pshersby/HP-Cal/Data/Connector.PNG

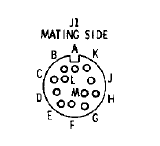
Data/Connector.PNG
