pshersby/HP-Cal/Data/Voltage divider.JPG

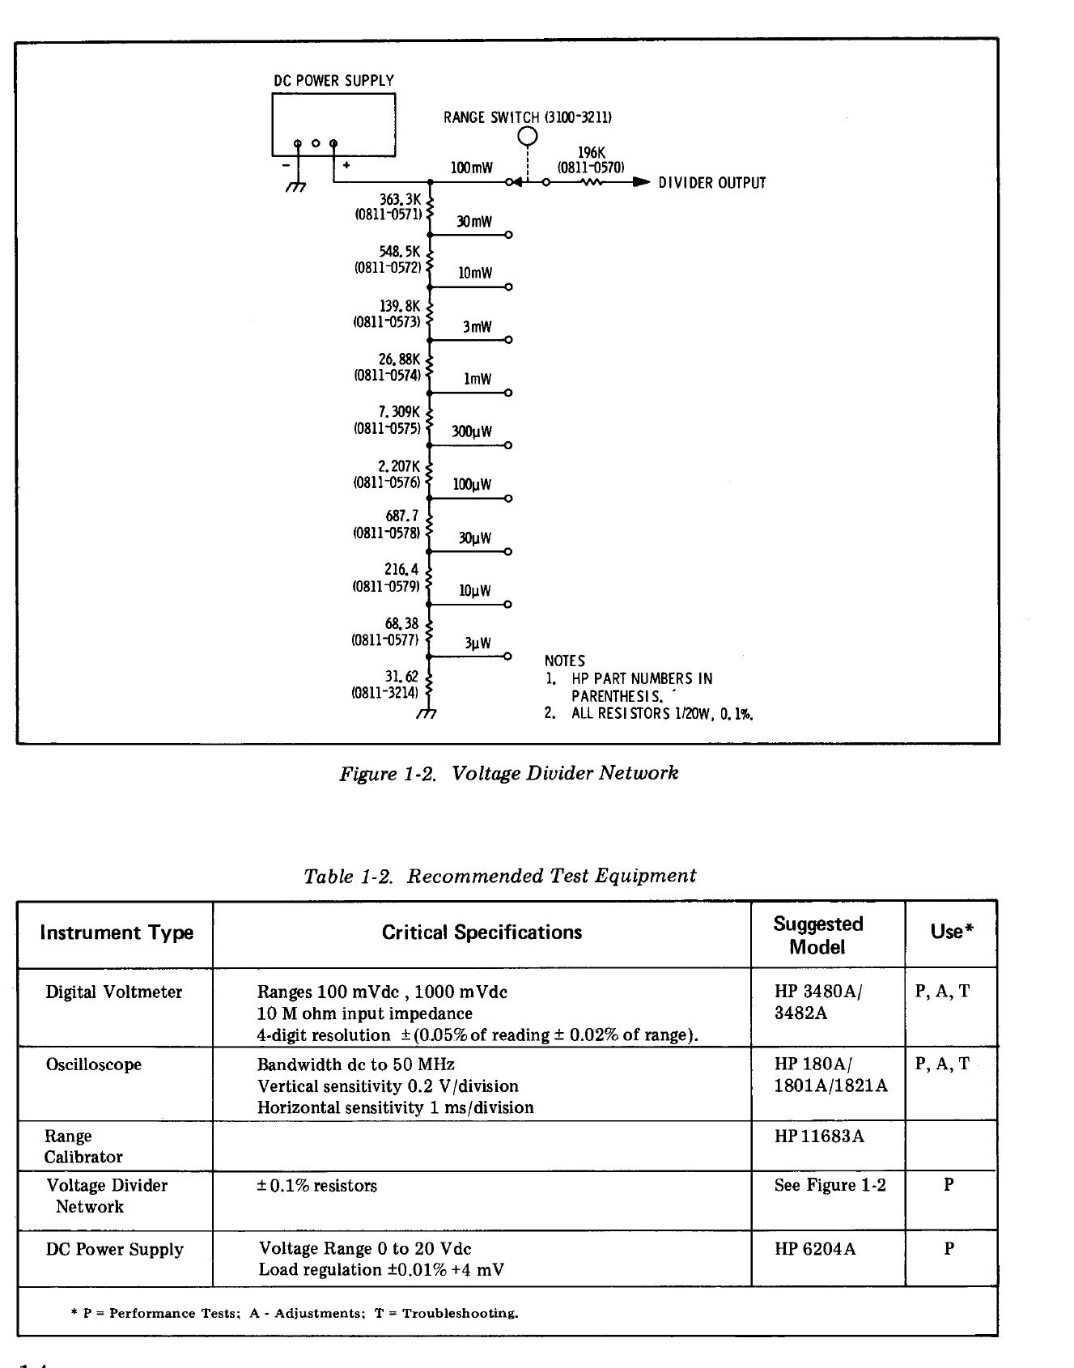
Data/Voltage divider.JPG
