pshersby/HP-Cal/DividerSimulation.cir

[Main]
FileType=CIR
Version=12.00
Program=Micro-Cap
Component Version=10.00
Shape Version=11.00
Screen=2560,1440
MCAPVersion=12.0.2.1
Key ID=Demo
NLCnt=43
TXCnt=4

[shapedef]
Name=Battery
Line=0,0,22,0
Line=22,-3,22,3
Line=26,-7,26,7
Line=26,0,48,0
Current=32,8,16,8

[shapedef]
Name=Ground
Line=0,0,12,0
Line=12,-8,12,8
Line=18,-4,18,4
Line=24,0,24,0

[shapedef]
Name=Resistor
PolyOpen=12
PolyLine=0,0
PolyLine=0,0
PolyLine=12,0
PolyLine=14,-4
PolyLine=18,4
PolyLine=22,-4
PolyLine=26,4
PolyLine=30,-4
PolyLine=34,4
PolyLine=36,0
PolyLine=48,0
PolyLine=48,0
Current=32,8,16,8

[compdef]
Name=Resistor
Definition=Resistor
Shape=Resistor
Mask=7425
Used=162
memo=Resistor
Label Offset=18,6,8,11
PinCnt=2
Pin="Plus",6,0,-10,-4
Pin="Minus",0,0,-14,-4

[compdef]
Name=Ground
Definition=Ground
Shape=Ground
Mask=1793
Used=259
memo=Ground
Label Offset=0,0,0,0
PinCnt=1
Pin="PinA",0,0,-3,-7

[compdef]
Name=Battery
Definition=Battery
Shape=Battery
Mask=6913
Used=52
memo=Battery
Label Offset=19,7,10,13
PinCnt=2
Pin="Plus",6,0,-4,-5
Pin="Minus",0,0,-10,-5

[Circuit]
Window Placement=2,3, -1,-1, -8,-31, 0,0,1961,813
Default Object=Color=#000080
Default Object Font=Height=-15,FStyle=0,Color=#000080,Name=Arial
Default Object Apply Border To Text=No
Default Object Apply Fill To Text=No
Default Object GridSnap=No
NodeVoltageFormat=3
CurrentFormat=3
PowerFormat=3
PathDelayFormat=3
WarningFormat=3
GridTextFormulaFormat=3
Window Placement in Transient Analysis=2,3, -1,-1, -8,-31, 0,0,1961,813
Window Placement in DC Analysis=2,3, -1,-1, -8,-31, 26,26,2187,824
SpiceType=AMBIGUOUS
Title_Block_Border=None
Title_Block=False
Show Nodes=False
Show Voltages=False
Show Current=False
Show Power=False
Show Condition=False
Show Pin Connections=False
Show Connection Warnings=False
Show Cross=False
Show Attribute Text=True
Show Grid Text=True

[Comp]
Name=Resistor
Px=832,280
Rot=3

[Attr]
ON=-24,-25,PART
V=R1
Style=8192

[Attr]
ON=-51,-39,RESISTANCE
V=363.3k
Style=8192

[Attr]
ON=0,0,PACKAGE
V

[Comp]
Name=Resistor
Px=832,352
Rot=3

[Attr]
ON=-24,-25,PART
V=R2
Style=8192

[Attr]
ON=-51,-39,RESISTANCE
V=548.5k
Style=8192

[Attr]
ON=0,0,PACKAGE
V

[Comp]
Name=Resistor
Px=832,440
Rot=3

[Attr]
ON=-24,-25,PART
V=R3
Style=8192

[Attr]
ON=-51,-39,RESISTANCE
V=139.8k
Style=8192

[Attr]
ON=0,0,PACKAGE
V

[Comp]
Name=Resistor
Px=832,528
Rot=3

[Attr]
ON=-24,-25,PART
V=R4
Style=8192

[Attr]
ON=-51,-39,RESISTANCE
V=26.88k
Style=8192

[Attr]
ON=0,0,PACKAGE
V

[Comp]
Name=Resistor
Px=832,608
Rot=3

[Attr]
ON=-24,-25,PART
V=R5
Style=8192

[Attr]
ON=-51,-39,RESISTANCE
V=7.309k
Style=8192

[Attr]
ON=0,0,PACKAGE
V

[Comp]
Name=Resistor
Px=832,704
Rot=3

[Attr]
ON=-24,-25,PART
V=R6
Style=8192

[Attr]
ON=-51,-39,RESISTANCE
V=2.207k
Style=8192

[Attr]
ON=0,0,PACKAGE
V

[Comp]
Name=Resistor
Px=832,800
Rot=3

[Attr]
ON=-24,-25,PART
V=R7
Style=8192

[Attr]
ON=-44,-39,RESISTANCE
V=687.7
Style=8192

[Attr]
ON=0,0,PACKAGE
V

[Comp]
Name=Resistor
Px=832,896
Rot=3

[Attr]
ON=-24,-25,PART
V=R8
Style=8192

[Attr]
ON=-44,-39,RESISTANCE
V=216.4
Style=8192

[Attr]
ON=0,0,PACKAGE
V

[Comp]
Name=Resistor
Px=832,984
Rot=3

[Attr]
ON=-24,-25,PART
V=R9
Style=8192

[Attr]
ON=-44,-39,RESISTANCE
V=68.38
Style=8192

[Attr]
ON=0,0,PACKAGE
V

[Comp]
Name=Resistor
Px=832,1072
Rot=3

[Attr]
ON=-32,-25,PART
V=R10
Style=8192

[Attr]
ON=-44,-39,RESISTANCE
V=31.62
Style=8192

[Attr]
ON=0,0,PACKAGE
V

[Wire]
Pxs=832,280,832,304

[Wire]
Pxs=832,352,832,392

[Wire]
Pxs=832,440,832,480

[Wire]
Pxs=832,528,832,560

[Wire]
Pxs=832,608,832,656

[Wire]
Pxs=832,704,832,752

[Wire]
Pxs=832,800,832,848

[Wire]
Pxs=832,896,832,936

[Wire]
Pxs=832,984,832,1008

[Comp]
Name=Resistor
Px=1080,280
Rot=5

[Attr]
ON=8,-25,PART
V=R11
Style=8192

[Attr]
ON=8,-39,RESISTANCE
V=196k
Style=8192

[Attr]
ON=0,0,PACKAGE
V

[Comp]
Name=Ground
Px=832,1072
Rot=7

[Comp]
Name=Ground
Px=560,1088
Rot=7

[Comp]
Name=Battery
Px=560,632
Rot=3

[Attr]
ON=-26,-27,PART
V=V1
Style=8192

[Attr]
ON=-38,-41,VALUE
V=15.8
Style=8192

[Attr]
ON=0,0,PACKAGE
V

[Wire]
Pxs=560,632,560,1088

[Wire]
Pxs=560,232,560,584

[Wire]
Pxs=560,232,832,232

[Wire]
Pxs=832,1008,1016,1008

[Wire]
Pxs=1016,232,1016,1008

[Comp]
Name=Resistor
Px=1192,1024
Rot=5

[Attr]
ON=8,-25,PART
V=R12
Style=8192

[Attr]
ON=8,-39,RESISTANCE
V=100Meg
Style=8192

[Attr]
ON=0,0,PACKAGE
V

[Wire]
Pxs=832,1072,1080,1072

[Wire]
Pxs=1192,1024,1192,1072

[Wire]
Pxs=1192,232,1192,976

[Wire]
Pxs=1016,232,1080,232

[Wire]
Pxs=1080,232,1192,232

[Comp]
Name=Resistor
Px=1080,376
Rot=5

[Attr]
ON=8,-25,PART
V=R13
Style=8192

[Attr]
ON=8,-39,RESISTANCE
V=15
Style=8192

[Attr]
ON=0,0,PACKAGE
V

[Comp]
Name=Resistor
Px=1080,608
Rot=5

[Attr]
ON=8,-25,PART
V=R14
Style=8192

[Attr]
ON=8,-39,RESISTANCE
V=196
Style=8192

[Attr]
ON=0,0,PACKAGE
V

[Wire]
Pxs=1080,280,1080,328

[Wire]
Pxs=1080,376,1080,560

[Wire]
Pxs=1080,1072,1192,1072

[Wire]
Pxs=832,1008,832,1024

[Wire]
Pxs=1016,1008,1016,1024

[Wire]
Pxs=1080,608,1080,1072

[Wire]
Pxs=1192,232,1424,232

[Grid Text]
Text="These are the 3 resistors on input to the chopper"
Px=1144,568
Angle=90
GridSnap=True
JustifyH=Left
JustifyV=Bottom
CBorder=None

[Grid Text]
Text="Move this link wire"
Text="to switch the range"
Px=864,976
GridSnap=True
JustifyH=Left
JustifyV=Bottom
CBorder=None

[Grid Text]
Text="=V(Vout)"
Px=1304,232
Height=-21
GridSnap=True
JustifyH=Left
JustifyV=Bottom
CBorder=None

[Grid Text]
Text="Vout"
Px=1192,232
GridSnap=True
JustifyH=Left
JustifyV=Bottom
CBorder=None

[Schematic]
CurrentSection 0=0
CurrentSection 1=0
CurrentSection 2=0
CurrentSection 3=0
Splitter.xs=0
Splitter.ys=0
TextQuad=4099
Scale=1
GridUser=10
ShapeGroups="Main","Euro","Polarity","Main1","Main11","Electrolytic","GroundArrow","DeMorgan"
CalcRMS=False
CalcAVG=False
CalcPeak=False
CalcVoltage=True
DisplayMeasure=Last
ShareScales=True

[Tools]
Pos=Top
FILESAVEASOLD=No
BOM=No
FILEPCB=No
PROBE=Yes
SELECT=Yes
PAN=Yes
COMP=Yes
TEXT=Yes
WIRE=Yes
WIRED=Yes
BUS=Yes
GRAPHIC=Yes
FLOWCHART=Yes
LINE=No
ELLIPSE=No
RECT=No
DIAM=No
ARC=No
PIE=No
TRIANGLE=No
STAR=No
LEFTBRK=No
RIGHTBRK=No
BOTHBRK=No
META=Yes
PARALLELOGRAM=No
FC_PROCESS=No
FC_ALT_PROCESS=No
FC_DECISION=No
FC_DATA=No
FC_PREDEFPROCESS=No
FC_INTERNALSTORAGE=No
FC_DOCUMENT=No
FC_MULTIDOCUMENT=No
FC_TERMINATOR=No
FC_PREPARATION=No
FC_MANUALINPUT=No
FC_MANUALOPERATION=No
FC_CONNECTOR=No
FC_OFFPAGECONNECTOR=No
FC_PUNCHCARD=No
FC_PUNCHEDTAPE=No
FC_SUMMING_JUNCTION=No
FC_OR=No
FC_COLLATE=No
FC_SORT=No
FC_EXTRACT=No
FC_MERGE=No
FC_STORED_DATA=No
FC_DELAY=No
FC_SAS=No
FC_MAGNETIC_DISK=No
FC_DAS=No
FC_DISPLAY=No
SPREAD_SHEET=Yes
POLYCLOS=No
POLYOPEN=No
FLAG=Yes
INFO=Yes
HELP=Yes
HELP_SPICE=No
LINK=Yes
CHECK=Yes
REGION_ENABLE=Yes
TITLE_BLOCK=Yes
DIGTRC=No
DIGTRC2=No
BUILD_COMMAND=Yes
DIGALL=No
GRIDTEXT=Yes
COMPTEXT=Yes
NODE=Yes
MEASURED=Yes
NODEV=Yes
CURRENT=Yes
POWER=Yes
CONDITIN=Yes
PIN=Yes
CONNWARN=Yes
CROSS=Yes
GRID=Yes
BORDER=Yes
BORDERONE=Yes
TITLE=Yes
RUBBER=Yes
PROPERTY=Yes
STEP=Yes
MIRROR=Yes
ROTATE=Yes
FLIPY=Yes
FLIPX=Yes
CIR_MAKEMACRO=No
CLEARCUTWIRE=No
CLIPBOARDCIRPAGE2BMM=No
FINDCOMP=Yes
FIND=Yes
REPEAT=No
REPLACE=No
MODEL=Yes
CIR2CKT=Yes
ATTDISP=Yes
ENABLE=Yes
DISABLE=Yes
ENABLE_WITH=Yes
TOFRONT=Yes
TOBACK=Yes
SELNEXT=Yes
PAGEADD=Yes
PAGEADDTEXT=No
ADDSECTION=No
PAGEDEL=Yes
ZOOMIN=Yes
ZOOMOUT=Yes
AUTOSCALECIR=Yes
GOTOFLAG=Yes
UPLEVEL=Yes
COLOR=Yes
FONT=Yes
STYLE=Yes
DM_LAST=No
DM_RMS=No
DM_AVG=No
DM_PEAK=No
GRID_NONE=No
GRID_NORMAL=No
GRID_BOLD_5=No
GRID_BOLD_6=No
GRID_BOLD_USER=No
GRAPH_PAPER=No
SPLITCIRTEXTH=No
SPLITCIRTEXTV=No
SPACE_SPLITTERS_EVENLY=No
NORMALCIR=No
RENAMEDEFINE=No
RENAMECMP=No
ATTALIGN=No
RESETNODEPOS=No
FIT2STANDARD=No
NODESNAP=No
MOVETEXT=No
TEXTINC=No
TOGGLETEXT=No
TOGGLEMODE=No
TOLERANCE=No
ALIGNAB=No
ALIGNLEFT=Yes
ALIGNCENTER=Yes
ALIGNRIGHT=Yes
ALIGNTOP=Yes
ALIGNMIDDLES=Yes
ALIGNBOTTOM=Yes

[Section]
Index=0
Name="circuit1"
Type=Main
Enable=True
CurrentPage 0=0
CurrentPage 1=0
CurrentPage 2=0
CurrentPage 3=0
TabSize 0=425
TabSize 1=425
TabSize 2=425
TabSize 3=425

[Page]
Index=0
Section=0
Print=True
Enable=True
Name=Main
PrinterScale=1
Scale 0=1
Scale 1=1
Scale 2=1
SB 3=0,48
Scale 3=1
Px=318,735
WinBackGround Color=#FFFFFF
Select Color=#FF0000
Anchor Color=#000000
Select Box Color=#000080
Grid Text Color=Height=-12,FStyle=0,Color=#0000FF,Name=Verdana
Grid Text RTF=False
Grid Text Angle=0
Grid Text GridSnap=True
Grid Text PinIt=False
Grid Text JustifyH=Left
Grid Text JustifyV=Bottom
Grid GradientColor2=None
Grid OutlineThickness=1
Grid OutlineColor=None
Component Color=#0000FF
Attribute Text=Height=-12,FStyle=0,Color=#008000,Name=Verdana
Wire Color=#008000
Bus Color=#008000
Pin Connection=Height=-10,FStyle=0,Color=#FF0000,Name=Arial
Pin Marker Color=#008000
Node Number=Height=-11,FStyle=0,Color=#FF00FF,Name=Arial
Node Voltage Color=Height=-11,FStyle=0,Color=#000000,Name=Arial
Dynamic AC Voltage Color=#E4E4E4
Text Banner Text=Height=-15,FStyle=0,Color=#800000,Name=Arial
Title Block Background=#C0C0C0
Current=Height=-11,FStyle=0,Color=#0000FF,Name=Arial
Power/Condition=Height=-11,FStyle=0,Color=#FF0000,Name=Arial
Digital Path Color=#FF0000
Title Block Border=#000000
Disabled	Color=#C0C0C0
Search Color=#FFFF00
Grid Color=#000000
Graph Paper=#E4E4E4
Digital 0 Color=#000000
Digital R Color=#FFFF00
Digital F Color=#FFFF00
Digital 1 Color=#FF0000
Digital X Color=#C0C0C0
Digital Z Color=#808080
Block Select Color=#51F998

[Page]
Index=1
Section=0
Type=Text
Print=False
Enable=True
Name=Text
Font=Height=-15,FStyle=0,Color=#000000,Name=Courier New
Comment Color=#008000
WinBackGround Color=#FFFFFF
Disabled	Color=#C0C0C0
KeyWord Color=#0000FF
Error	Color=#FF0000
Search Color=#FFFF00

[Page]
Index=2
Section=0
Type=Text
Print=False
Enable=True
Name=Models
Font=Height=-15,FStyle=0,Color=#000000,Name=Courier New
Comment Color=#008000
WinBackGround Color=#FFFFFF
Disabled	Color=#C0C0C0
KeyWord Color=#0000FF
Error	Color=#FF0000
Search Color=#FFFF00

[Page]
Index=3
Section=0
Type=Info
Print=False
Enable=True
Name=Info
Font=Height=-15,FStyle=0,Color=#000000,Name=Courier New
Comment Color=#008000
WinBackGround Color=#FFFFFF
Disabled	Color=#C0C0C0
KeyWord Color=#0000FF
Error	Color=#FF0000
Search Color=#FFFF00

[Text Area]
Section=0
Page=1

[Text Area]
Section=0
Page=2

[InfoPage]
InfoPage=True
Warnings=True
System=True
Defines=True
Array=True
Model=True
Measure=True
MacroSubckt=True
NotUsed=True
ComponentCounts=True
VariablizePaths=False
DontShowPaths=False
SimulationLog=True

[Transient]
WinID=1
Window Placement=2,3, -1,-1, -8,-31, 0,0,1961,813
Font=Height=-19,FStyle=0,Color=#0000FF,Name=Arial
WinBackGround Color=#FFFFFF
Select Color=#FF0000
Anchor Color=#000000
Select Box Color=#000080
Title
AutoTitle=Yes
Grid Color=#808080
Grid Weight=1
Grid Pattern=Dot6
Tracker Foreground=Height=-15,FStyle=0,Color=#000000,Name=Arial
Tracker Background=#FFFF00
Baseline color=#0000FF
BaseLine Weight=1
CurveFit color=#FF0000
CurveFit Weight=2
CurveFit Pattern=Dash
Static Grids=False
PlusMark=False
MinorLog25=Off
LabelMinor=Off
DataPoints=False
Token=False
Ruler=False
XAxisGrids=True
YAxisGrids=True
MinorLogGrids=True
BaseLine=False
AlignZ=True
Align Cursors=True
TagFormatX=3
TagFormatY=3
FormulaFormat=2
EndMode=SCALE
Graph Background=#FFFFFF
Tracker Intercept=False
Tracker Mouse=True
Tracker Cursor=True
Tracker Cursor BranchInfo=False
Horizontal Cursor=False
Same Y Scales=Yes
Enable X Scaling=True
Enable Y Scaling=True
Keep X Scales The Same=True
Number of Grids X=5
Number of Grids Y=5
Cursor Select Color Primary=#C0C0C0
Cursor Select Color Secondary=#FF0000
Data Point Labels Color Fore=Height=-15,FStyle=0,Color=#000000,Name=Arial
Data Point Labels Color Back=#FFFF00
OperPoint=True
OperPointOnly=False
AutoScaleRanges=True
FixedTimeStep=False
DoPSS=False
PSS_Periods="1"
PSS_Iterations="5"
PSS_Error="1u"
PSS_ShowPlots=True
FFT_NPts="8192"
FFT_IncludeDCHarmonic=False
FFT_AutoScale_Harmonics="10"
PrinterAutoTile=No
PrinterBlackBorder=No
MonMaxShow=3
MonPageWidth=66
MonPlotWidth=21
MonExprXWidth=142
MonExprYWidth=367
MonRangeXWidth=90
MonRangeYWidth=90
AnimateWait=None
AnimateWaitTime=500
AnimatePressAfter=0
Save_For_Future=No
Reduce_Display=1
Reduce_Save=1
Reduce_ThrowDataOut=0
Num Out Header Left
Num Out Header Center="$MC\n$user\n$company\n$Analysis of $name\n$date $time"
Num Out Header Right
Num Out Delimiter=32
Num Out Write=True
Num Out Write Main Header=True
Num Out Write Limits=True
Num Out Write Branch Header=True
Num Out Write Models=False
Num Out Write Zero Models=True
Num Out Write Undefined Models=True
Num Out Write Operating Point=True
Num Out Write Measurement Values=True
Num Out Write Tolerance Detail=True
Num Out Write Values=True
Num Out Write Waveform Header=True
Num Out Allow Dup Y Expr=False
Num Out Low="TSTART"
Num Out High="TMAX"
Num Out Font=Height=-15,FStyle=0,Color=#000000,Name=Courier New
Num Out Format=3
Num Out HideNonSelected=False
Num Out UseActualDataPoints=False
AutoSaveWave=False
Wave Format=16E
State Variables Format=5E
Print Individual Pages=False

[Tools]
Pos=Top
SELECT=Yes
PAN=Yes
GRAPHIC=Yes
LINE=No
ELLIPSE=No
RECT=No
DIAM=No
ARC=No
PIE=No
TRIANGLE=No
STAR=No
LEFTBRK=No
RIGHTBRK=No
BOTHBRK=No
META=Yes
PARALLELOGRAM=No
POLYCLOS=No
POLYOPEN=No
SCALE=Yes
CURSOR=Yes
MEASUREH=Yes
MEASUREV=Yes
TAG=Yes
PTAG=Yes
TEXT=Yes
PROPERTY=Yes
START=Yes
STOP=Yes
PAUSE=Yes
RESUME=No
DATAPTS=Yes
TOKENS=Yes
RULER=Yes
PLUS=Yes
XAXIS=Yes
YAXIS=Yes
MINORLOG=Yes
LOG25=Yes
BASELINE=Yes
HORIZCUR=Yes
GOTOX=Yes
GOTOY=Yes
GOTOPERF=Yes
GOTOBRNC=Yes
CLEAR_ACCUMULATED=Yes
PDELETE_ALL_PLOTS=Yes
NEXT=Yes
NEXTIN=Yes
PEAK=Yes
VALLEY=Yes
HIGH=Yes
LOW=Yes
INFLECTN=Yes
GHIGH=Yes
GLOW=Yes
BOTTOM=Yes
TOP=Yes
WAVEFORMBUFFER=Yes
AOUTPUT=Yes
PKEY=Yes
ENXSCALE=Yes
ENYSCALE=Yes
ZOOMIN=Yes
ZOOMOUT=Yes
AUTOSCALE=Yes
RESTORESCALE=No
COLOR=Yes
FONT=Yes
STYLE=Yes
SELNEXT=Yes
NORMALIZE=No
NORMALIZE_MIN=No
NORMALIZE_MAX=No
ADD_TAG_LEFT=No
ADD_TAG_RIGHT=No
ADD_HORZ_TAG=No
ADD_VERT_TAG=No
ALIGN_CURSORS=No
ALIGN_CURSORSZ=No
CURSORTOCLIPBOARD=No
TRACKER_CURSOR=No
TRACKER_CURSOR_BRANCHINFO=No
TRACKER_INTERCEPT=No
TRACKER_MOUSE=No
TOFRONT=Yes
TOBACK=Yes
SPLITCIRTEXTH=No
SPLITCIRTEXTV=No
SPACE_SPLITTERS_EVENLY=No
NORMALCIR=No
LABEL_WAVEFORM=No
LABEL_DATA_POINTS=No
WFB_ADD_TO_LIMITS=No
ENVELOPE=No
SAMEYSCALES=No
KEEPXSCALESTHESAME=No
CURVEFIT=No
ADD_MARKER=No
SHOWWATCH=No
BP=No
TOGGLEMODE=No
REMOVEALLTEXT=No
AUTOSCALEX=No
LABELALLMINOR=No
ALIGNLEFT=Yes
ALIGNCENTER=Yes
ALIGNRIGHT=Yes
ALIGNTOP=Yes
ALIGNMIDDLES=Yes
ALIGNBOTTOM=Yes

[APage]
Analysis=Transient
Name="MAIN"

[DC]
WinID=3
Window Placement=2,3, -1,-1, -8,-31, 26,26,2187,824
Font=Height=-19,FStyle=0,Color=#0000FF,Name=Arial
WinBackGround Color=#FFFFFF
Select Color=#FF0000
Anchor Color=#000000
Select Box Color=#000080
Title
AutoTitle=Yes
Grid Color=#808080
Grid Weight=1
Grid Pattern=Dot6
Tracker Foreground=Height=-15,FStyle=0,Color=#000000,Name=Arial
Tracker Background=#FFFF00
Baseline color=#0000FF
BaseLine Weight=1
CurveFit color=#FF0000
CurveFit Weight=2
CurveFit Pattern=Dash
Static Grids=False
PlusMark=False
MinorLog25=Off
LabelMinor=Off
DataPoints=False
Token=False
Ruler=False
XAxisGrids=True
YAxisGrids=True
MinorLogGrids=True
BaseLine=False
AlignZ=True
Align Cursors=True
TagFormatX=3
TagFormatY=3
FormulaFormat=2
EndMode=SCALE
Graph Background=#FFFFFF
Tracker Intercept=False
Tracker Mouse=True
Tracker Cursor=True
Tracker Cursor BranchInfo=False
Horizontal Cursor=False
Same Y Scales=Yes
Enable X Scaling=True
Enable Y Scaling=True
Keep X Scales The Same=True
Number of Grids X=5
Number of Grids Y=5
Cursor Select Color Primary=#C0C0C0
Cursor Select Color Secondary=#FF0000
Data Point Labels Color Fore=Height=-15,FStyle=0,Color=#000000,Name=Arial
Data Point Labels Color Back=#FFFF00
AutoScaleRanges=True
PrinterAutoTile=No
PrinterBlackBorder=No
MonMaxShow=2
MonPageWidth=66
MonPlotWidth=21
MonExprXWidth=142
MonExprYWidth=286
MonRangeXWidth=90
MonRangeYWidth=90
AnimateWait=None
AnimateWaitTime=500
AnimatePressAfter=0
Save_For_Future=No
Reduce_Display=1
Reduce_Save=1
Reduce_ThrowDataOut=0
Num Out Header Left
Num Out Header Center="$MC\n$user\n$company\n$Analysis of $name\n$date $time"
Num Out Header Right
Num Out Delimiter=32
Num Out Write=True
Num Out Write Main Header=True
Num Out Write Limits=True
Num Out Write Branch Header=True
Num Out Write Models=False
Num Out Write Zero Models=True
Num Out Write Undefined Models=True
Num Out Write Measurement Values=True
Num Out Write Tolerance Detail=True
Num Out Write Values=True
Num Out Write Waveform Header=True
Num Out Allow Dup Y Expr=False
Num Out Low="DCMIN"
Num Out High="DCMAX"
Num Out Font=Height=-15,FStyle=0,Color=#000000,Name=Courier New
Num Out Format=3
Num Out HideNonSelected=False
Num Out UseActualDataPoints=False
AutoSaveWave=False
Wave Format=16E
State Variables Format=5E
Print Individual Pages=False

[Tools]
Pos=Top
SELECT=Yes
PAN=Yes
GRAPHIC=Yes
LINE=No
ELLIPSE=No
RECT=No
DIAM=No
ARC=No
PIE=No
TRIANGLE=No
STAR=No
LEFTBRK=No
RIGHTBRK=No
BOTHBRK=No
META=Yes
PARALLELOGRAM=No
POLYCLOS=No
POLYOPEN=No
SCALE=Yes
CURSOR=Yes
MEASUREH=Yes
MEASUREV=Yes
TAG=Yes
PTAG=Yes
TEXT=Yes
PROPERTY=Yes
START=Yes
STOP=Yes
PAUSE=Yes
RESUME=No
DATAPTS=Yes
TOKENS=Yes
RULER=Yes
PLUS=Yes
XAXIS=Yes
YAXIS=Yes
MINORLOG=Yes
LOG25=Yes
BASELINE=Yes
HORIZCUR=Yes
GOTOX=Yes
GOTOY=Yes
GOTOPERF=Yes
GOTOBRNC=Yes
CLEAR_ACCUMULATED=Yes
PDELETE_ALL_PLOTS=Yes
NEXT=Yes
NEXTIN=Yes
PEAK=Yes
VALLEY=Yes
HIGH=Yes
LOW=Yes
INFLECTN=Yes
GHIGH=Yes
GLOW=Yes
BOTTOM=Yes
TOP=Yes
WAVEFORMBUFFER=Yes
AOUTPUT=Yes
PKEY=Yes
ENXSCALE=Yes
ENYSCALE=Yes
ZOOMIN=Yes
ZOOMOUT=Yes
AUTOSCALE=Yes
RESTORESCALE=No
COLOR=Yes
FONT=Yes
STYLE=Yes
SELNEXT=Yes
NORMALIZE=No
NORMALIZE_MIN=No
NORMALIZE_MAX=No
ADD_TAG_LEFT=No
ADD_TAG_RIGHT=No
ADD_HORZ_TAG=No
ADD_VERT_TAG=No
ALIGN_CURSORS=No
ALIGN_CURSORSZ=No
CURSORTOCLIPBOARD=No
TRACKER_CURSOR=No
TRACKER_CURSOR_BRANCHINFO=No
TRACKER_INTERCEPT=No
TRACKER_MOUSE=No
TOFRONT=Yes
TOBACK=Yes
SPLITCIRTEXTH=No
SPLITCIRTEXTV=No
SPACE_SPLITTERS_EVENLY=No
NORMALCIR=No
LABEL_WAVEFORM=No
LABEL_DATA_POINTS=No
WFB_ADD_TO_LIMITS=No
ENVELOPE=No
SAMEYSCALES=No
KEEPXSCALESTHESAME=No
CURVEFIT=No
ADD_MARKER=No
SHOWWATCH=No
BP=No
TOGGLEMODE=No
REMOVEALLTEXT=No
AUTOSCALEX=No
LABELALLMINOR=No
ALIGNLEFT=Yes
ALIGNCENTER=Yes
ALIGNRIGHT=Yes
ALIGNTOP=Yes
ALIGNMIDDLES=Yes
ALIGNBOTTOM=Yes

[Monte Carlo Options]
Analysis=Transient
Status=Off
Zero Tolerance=False
Eliminate Outliers=False
Distribution=Normal
Number of Runs=10
Seed=0

[Monte Carlo Options]
Analysis=DC
Status=Off
Zero Tolerance=False
Eliminate Outliers=False
Distribution=Normal
Number of Runs=10
Seed=0

[Limits]
Analysis=Transient
TMax=1u
TStart=0
TStep=0
NPts=51
Temp=27
RetraceRuns=1
StateVar=Zero
RunOption=Normal
Temperature Type=Linear
Accumulate Plots=False
IgnoreExprErrors=False

[WaveForm]
Analysis=Transient
Plt=1
AliasID=1
XExp=T
YExp=v(Vout)
XRng=1e-6
YRng=40
Options=LINEARX,LINEARY
Range Grid X=2e-7
Range Grid Y=8
Enable=Enable
Line Color=#0000FF
Text Color=#0000FF
Rainbow=False
VFmtX=3
VFmtY=3
ScaleFactorX="None"
ScaleFactorY="None"
ScaleUnitsX="Auto"
ScaleUnitsY="Auto"
SFmtX=2
SFmtY=2
NOFmtX=3E
NOFmtY=3E

[WaveForm]
Analysis=Transient
Plt=1
AliasID=2
XExp=T
YExp=v(1)
XRng=1e-6
YRng=40
Options=LINEARX,LINEARY
Range Grid X=2e-7
Range Grid Y=8
Enable=Enable
Line Color=#FF0000
Text Color=#FF0000
Rainbow=False
VFmtX=3
VFmtY=3
ScaleFactorX="None"
ScaleFactorY="None"
ScaleUnitsX="Auto"
ScaleUnitsY="Auto"
SFmtX=2
SFmtY=2
NOFmtX=3E
NOFmtY=3E

[WaveForm]
Analysis=Transient
AliasID=-1
Options=LINEARX,LINEARY
Enable=Enable
Line Color=#008000
Text Color=#008000
Rainbow=False
VFmtX=3
VFmtY=3
ScaleFactorX="None"
ScaleFactorY="None"
ScaleUnitsX="Auto"
ScaleUnitsY="Auto"
SFmtX=2
SFmtY=2
NOFmtX=3E
NOFmtY=3E

[Limits]
Analysis=DC
I1Range=10,0,.5
NPts=51
Temp=27
MaxChng=5
StateVar=Zero
RunOption=Normal
Temperature Type=Linear
Accumulate Plots=False
IgnoreExprErrors=False
Sweep1 type=Auto
Sweep2 type=None

[WaveForm]
Analysis=DC
AliasID=-1
Options=LINEARX,LINEARY
Enable=Enable
Line Color=#FF0000
Text Color=#FF0000
Rainbow=False
VFmtX=3
VFmtY=3
ScaleFactorX="None"
ScaleFactorY="None"
ScaleUnitsX="Auto"
ScaleUnitsY="Auto"
SFmtX=2
SFmtY=2
NOFmtX=3E
NOFmtY=3E

[WaveForm]
Analysis=DC
AliasID=-1
Options=LINEARX,LINEARY
Enable=Enable
Line Color=#008000
Text Color=#008000
Rainbow=False
VFmtX=3
VFmtY=3
ScaleFactorX="None"
ScaleFactorY="None"
ScaleUnitsX="Auto"
ScaleUnitsY="Auto"
SFmtX=2
SFmtY=2
NOFmtX=3E
NOFmtY=3E

[Limits]
Analysis=DynamicAC
FirstValueDisplay=Mag
SecondValueDisplay=PhaseDeg
PlaceText=True

[Limits]
Analysis=DynamicDC
PlaceText=True

[Pane]
Analysis=Transient
CurrentPage 0="MAIN"

[Pane]
Analysis=AC

[Pane]
Analysis=DC

[Pane]
Analysis=HmDistortion

[Pane]
Analysis=ImDistortion

[Pane]
Analysis=Stability

[Watch]
Analysis=Transient
Format=3
ExprPercentWidth=80

[Watch]
Analysis=DC
Format=3
ExprPercentWidth=80

[WCTolerance]
Var Width=100
Nominal Width=72
Tol Width=152
Tol Name=Drift
Col Width Neq=50
Col Width Pos=50
Col Width Rnd=50

[WCFiles]
UseFile=<Library>Standard.tlib
AVAILABLE_FILE=<Library>Standard.tlib

[OPMethods]
Analysis=Transient
Standard Newton-Raphson=0,0
Source Stepping=0,0
Diagonal Gmin Stepping=0,0
Junction Gmin Stepping=0,0
Pseudo Transient=0,0

[OPMethods]
Analysis=AC
Standard Newton-Raphson=0,0
Source Stepping=0,0
Diagonal Gmin Stepping=0,0
Junction Gmin Stepping=0,0
Pseudo Transient=0,0

[OPMethods]
Analysis=DC
Standard Newton-Raphson=0,0
Source Stepping=0,0
Diagonal Gmin Stepping=0,0
Junction Gmin Stepping=0,0
Pseudo Transient=0,0

[OPMethods]
Analysis=HmDistortion
Standard Newton-Raphson=0,0
Source Stepping=0,0
Diagonal Gmin Stepping=0,0
Junction Gmin Stepping=0,0
Pseudo Transient=0,0

[OPMethods]
Analysis=ImDistortion
Standard Newton-Raphson=0,0
Source Stepping=0,0
Diagonal Gmin Stepping=0,0
Junction Gmin Stepping=0,0
Pseudo Transient=0,0

[OPMethods]
Analysis=Stability
Standard Newton-Raphson=0,0
Source Stepping=0,0
Diagonal Gmin Stepping=0,0
Junction Gmin Stepping=0,0
Pseudo Transient=0,0

[OPMethods]
Analysis=DynamicAC
Standard Newton-Raphson=0,0
Source Stepping=0,0
Diagonal Gmin Stepping=0,0
Junction Gmin Stepping=0,0
Pseudo Transient=0,0

[OPMethods]
Analysis=DynamicDC
Standard Newton-Raphson=0,0
Source Stepping=0,0
Diagonal Gmin Stepping=0,0
Junction Gmin Stepping=0,0
Pseudo Transient=0,0
