pshersby/HP-Cal/sim.cir

[Main]
FileType=CIR
Version=12.00
Program=Micro-Cap
Component Version=10.00
Shape Version=11.00
Screen=2560,1440
MCAPVersion=12.0.2.1
Key ID=Demo
NLCnt=212
TXCnt=25

[shapedef]
Name=Battery
Line=0,0,22,0
Line=22,-3,22,3
Line=26,-7,26,7
Line=26,0,48,0
Current=32,8,16,8

[shapedef]
Name=Bjt.root
Line=0,0,13,0
Rectangle=13,-12,15,12
Current=32,-24,32,-16
Current=32,24,32,16
Current=0,-8,8,-8
PolyOpen=3
PolyLine=24,-24
PolyLine=24,-12
PolyLine=14,-2
PolyOpen=3
PolyLine=24,24
PolyLine=24,12
PolyLine=14,2

[shapedef]
Name=Capacitor
Line=0,0,22,0
Line=22,-8,22,8
Line=26,-8,26,8
Line=26,0,48,0
Current=32,12,16,12

[shapedef]
Name=Diode
Root="Diode.root",0,0,0

[shapedef]
Name=Diode.root
Line=0,0,20,0
Line=28,0,48,0
Rectangle=18,-8,20,8
PolyClosed=3
PolyLine=20,0
PolyLine=28,-8
PolyLine=28,8
Current=32,16,16,16

[shapedef]
Name=Ground
Line=0,0,12,0
Line=12,-8,12,8
Line=18,-4,18,4
Line=24,0,24,0

[shapedef]
Name=Jfet.root
Line=0,0,6,0
Line=14,-12,14,12
Line=14,-8,24,-8
Line=14,8,24,8
Ellipse=31,15,33,17
FColor=None
Line=24,8,24,24
Line=24,-8,24,-24
Line=10,0,14,0
Current=32,-24,32,-16
Current=32,24,32,16
Current=0,-8,8,-8

[shapedef]
Name=Minus.root
Line=-2,0,2,0

[shapedef]
Name=NJFET
PolyClosed=3
PolyLine=6,4
PolyLine=6,-4
PolyLine=10,0
Root="Jfet.root",0,0,0

[shapedef]
Name=NPN
Root="Bjt.root",0,0,0
PolyClosed=3
PolyLine=20,12
PolyLine=24,12
PolyLine=24,8

[shapedef]
Name=Opamp5
Root="Opamp.root",0,0,0
Root="Plus.root",25,-4,0
Root="Minus.root",25,52,0
Line=32,56,32,34
Line=32,-8,32,13

[shapedef]
Name=Opamp.root
Line=0,48,6,48
Line=0,0,5,0
Line=6,-4,6,52
Line=6,-4,48,24
Line=6,52,48,24
Line=48,24,72,24
Line=10,12,14,12
Line=12,10,12,14
Line=10,36,14,36
Line=4,0,6,0

[shapedef]
Name=Plus.root
Line=-2,0,2,0
Line=0,-2,0,2

[shapedef]
Name=Pulse_Source
Root="Vsource.root",0,0,0
Line=20,-4,20,0
Line=20,0,26,0
Line=26,0,26,4

[shapedef]
Name=Resistor
PolyOpen=12
PolyLine=0,0
PolyLine=0,0
PolyLine=12,0
PolyLine=14,-4
PolyLine=18,4
PolyLine=22,-4
PolyLine=26,4
PolyLine=30,-4
PolyLine=34,4
PolyLine=36,0
PolyLine=48,0
PolyLine=48,0
Current=32,8,16,8

[shapedef]
Name=Vsource.root
Line=0,0,12,0
Line=36,0,48,0
Ellipse=12,-12,36,12
FColor=None
Line=7,5,7,9
Root="Plus.root",41,7,0
Current=32,16,16,16

[shapedef]
Name=Zener
Root="Diode.root",0,0,0
Rectangle=16,-9,20,-8
Rectangle=18,8,22,9

[compdef]
Name=Resistor
Definition=Resistor
Shape=Resistor
Mask=7425
Used=162
memo=Resistor
Label Offset=18,6,8,11
PinCnt=2
Pin="Plus",6,0,-10,-4
Pin="Minus",0,0,-14,-4

[compdef]
Name=Capacitor
Definition=Capacitor
Shape=Capacitor
Mask=7425
Used=22
memo=Capacitor
Label Offset=16,12,12,12
PinCnt=2
Pin="Plus",6,0,-3,-5
Pin="Minus",0,0,-14,-5

[compdef]
Name=Opamp
Definition=Opamp
Shape=Opamp5
Mask=5121
Used=3
memo=Opamp
Label Offset=44,29,-14,39
PinCnt=5
Pin="Plus input",0,0,-31,-7
Pin="Minus input",0,6,-33,20
Pin="VEE",4,7,3,-5
Pin="Output",9,3,-13,-4
Pin="VCC",4,-1,5,14

[compdef]
Name=Battery
Definition=Battery
Shape=Battery
Mask=6913
Used=52
memo=Battery
Label Offset=19,7,10,13
PinCnt=2
Pin="Plus",6,0,-4,-5
Pin="Minus",0,0,-10,-5

[compdef]
Name=Ground
Definition=Ground
Shape=Ground
Mask=1793
Used=259
memo=Ground
Label Offset=0,0,0,0
PinCnt=1
Pin="PinA",0,0,-3,-7

[compdef]
Name=NPN
Definition=NPN
Shape=NPN
Mask=5633
Used=11
memo=NPN Transistor
Label Offset=37,-17,-14,33
PinCnt=3
Pin="Collector",3,-3,4,14
Pin="Base",0,0,-18,-3
Pin="Emitter",3,3,5,1

[compdef]
Name=Diode
Definition=Diode
Shape=Diode
Mask=5377
Used=10
memo=Diode
Label Offset=17,10,12,12
PinCnt=2
Pin="Anode",6,0,-9,-8
Pin="Cathode",0,0,-20,-8

[compdef]
Name=Zener
Definition=Diode
Shape=Zener
Mask=4096
memo=Zener diode
Label Offset=16,11,16,11
PinCnt=2
Pin="Anode",6,0,-14,-2
Pin="Cathode",0,0,-26,-2

[compdef]
Name=Pulse Source
Definition=Pulse source
Shape=Pulse_Source
Mask=4864
Used=7
memo=Pulse Source
Label Offset=18,13,15,9
PinCnt=2
Pin="Plus",6,0,-5,-4
Pin="Minus",0,0,-19,-4

[compdef]
Name=NJFET
Definition=NJFET
Shape=NJFET
Mask=4096
Used=5
memo=NJFET
Label Offset=37,-14,-8,35
PinCnt=3
Pin="Drain",3,-3,6,13
Pin="Gate",0,0,-19,-3
Pin="Source",3,3,6,4

[Circuit]
Window Placement=2,3, -1,-1, -8,-31, 0,0,1961,821
Default Object=Color=#000080
Default Object Font=Height=-15,FStyle=0,Color=#000080,Name=Arial
Default Object Apply Border To Text=No
Default Object Apply Fill To Text=No
Default Object GridSnap=No
NodeVoltageFormat=3
CurrentFormat=3
PowerFormat=3
PathDelayFormat=3
WarningFormat=3
GridTextFormulaFormat=3
Window Placement in Transient Analysis=0,1, -1,-1, -8,-31, 908,0,2546,1192
SpiceType=AMBIGUOUS
Title_Block_Border=None
Title_Block=False
Show Nodes=False
Show Voltages=False
Show Current=False
Show Power=False
Show Condition=False
Show Pin Connections=False
Show Connection Warnings=False
Show Cross=False
Show Attribute Text=True
Show Grid Text=True

[Object]
Object=Star
NumberOfPoints=5
CBorder=#000080
Px=1897,218,1987,293

[Object]
Object=Rectangle
CBorder=#000080
Pattern=Dot6
Px=1368,44,2245,927

[Comp]
Name=Resistor
Px=536,440
Rot=3

[Attr]
ON=-24,-25,PART
V=R1
Style=8192

[Attr]
ON=-24,-39,RESISTANCE
V=15
Style=8192

[Attr]
ON=0,0,PACKAGE
V

[Comp]
Name=Resistor
Px=736,536
Rot=3

[Attr]
ON=-24,-25,PART
V=R2
Style=8192

[Attr]
ON=-24,-39,RESISTANCE
V=15
Style=8192

[Attr]
ON=0,0,PACKAGE
V

[Comp]
Name=Resistor
Px=536,536
Rot=3

[Attr]
ON=-24,-25,PART
V=R3
Style=8192

[Attr]
ON=-32,-39,RESISTANCE
V=196
Style=8192

[Attr]
ON=0,0,PACKAGE
V

[Comp]
Name=Resistor
Px=352,360
Rot=4

[Attr]
ON=18,-20,PART
V=R4
Style=8192

[Attr]
ON=18,-34,RESISTANCE
V=196k
Style=8192

[Attr]
ON=0,0,PACKAGE
V

[Comp]
Name=Resistor
Px=600,288
Rot=3

[Attr]
ON=-24,-25,PART
V=R5
Style=8192

[Attr]
ON=-23,-39,RESISTANCE
V=1k
Style=8192

[Attr]
ON=0,0,PACKAGE
V

[Comp]
Name=Resistor
Px=800,288
Rot=3

[Attr]
ON=-24,-25,PART
V=R6
Style=8192

[Attr]
ON=-23,-39,RESISTANCE
V=1k
Style=8192

[Attr]
ON=0,0,PACKAGE
V

[Wire]
Pxs=536,360,536,392

[Wire]
Pxs=536,360,576,360

[Wire]
Pxs=400,360,528,360

[Wire]
Pxs=536,440,536,472

[Wire]
Pxs=624,360,736,360

[Wire]
Pxs=736,328,736,352

[Wire]
Pxs=736,424,736,448

[Wire]
Pxs=536,536,584,536

[Wire]
Pxs=600,288,600,336

[Wire]
Pxs=800,288,800,400

[Wire]
Pxs=760,400,800,400

[Comp]
Name=Capacitor
Px=736,328
Rot=5

[Attr]
ON=12,-26,PART
V=C1
Style=8192

[Attr]
ON=12,-40,CAPACITANCE
V=100p
Style=8192

[Attr]
ON=0,0,PACKAGE
V

[Comp]
Name=Capacitor
Px=624,424
Rot=5

[Attr]
ON=12,-26,PART
V=C2
Style=8192

[Attr]
ON=12,-40,CAPACITANCE
V=100p
Style=8192

[Attr]
ON=0,0,PACKAGE
V

[Wire]
Pxs=624,360,624,376

[Wire]
Pxs=624,424,624,448

[Wire]
Pxs=624,448,736,448

[Wire]
Pxs=736,192,736,280

[Wire]
Pxs=528,192,736,192

[Comp]
Name=Resistor
Px=976,192
Rot=4

[Attr]
ON=18,-20,PART
V=R7
Style=8192

[Attr]
ON=18,-34,RESISTANCE
V=464k
Style=8192

[Attr]
ON=0,0,PACKAGE
V

[Wire]
Pxs=528,192,528,360

[Wire]
Pxs=528,360,536,360

[Comp]
Name=Capacitor
Px=584,536
Rot=5

[Attr]
ON=12,-26,PART
V=C3
Style=8192

[Attr]
ON=12,-40,CAPACITANCE
V=47u
Style=8192

[Attr]
ON=0,0,PACKAGE
V

[Wire]
Pxs=584,536,736,536

[Wire]
Pxs=584,472,584,488

[Wire]
Pxs=536,472,584,472

[Wire]
Pxs=536,472,536,488

[Wire]
Pxs=736,192,976,192

[Wire]
Pxs=736,360,736,376

[Wire]
Pxs=736,448,736,488

[Comp]
Name=Capacitor
Px=928,352
Rot=6

[Attr]
ON=-33,12,PART
V=C4
Style=8192

[Attr]
ON=-44,26,CAPACITANCE
V=3.3u
Style=8192

[Attr]
ON=0,0,PACKAGE
V

[Wire]
Pxs=736,352,832,352

[Wire]
Pxs=736,352,736,360

[Comp]
Name=Opamp
Px=1480,328
Rot=4

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

[Wire]
Pxs=1920,560,1952,560

[Wire]
Pxs=1920,560,1920,760

[Wire]
Pxs=1624,760,1920,760

[Wire]
Pxs=2016,624,2016,656

[Wire]
Pxs=2016,656,2024,656

[Wire]
Pxs=1504,696,1624,696

[Wire]
Pxs=1504,728,1520,728

[Wire]
Pxs=1456,624,1456,784

[Wire]
Pxs=1456,784,1520,784

[Wire]
Pxs=832,352,880,352

[Grid Text]
Text="Note simulating with MMBFJ112 but 111 fitted in prototype"
Text="111  Idds = 20mA@15v , 50r RDS(On), 3v@1uA VGS(off) @ Id"
Text="112  Idds = 5mA@15v , 30r RDS(On), 1v@1uA VGS(off) @ Id"
Text=""
Text="MMBFJ110 may be best choice of this range"
Text="Consider using Dual JFET NSVJ6904DSB6 or similar"
Px=440,680
GridSnap=True
JustifyH=Left
JustifyV=Bottom
CBorder=None

[Grid Text]
Text="AC approx 100mV p-p at 0dBm"
Text="DC -900mv approx but"
Text="changes in some serial no"
Text="reduce to closer to 650mV"
Px=1992,272
GridSnap=True
JustifyH=Left
JustifyV=Bottom
CBorder=None

[Grid Text]
Text="1"
Px=1936,264
Height=-21
GridSnap=True
JustifyH=Left
JustifyV=Bottom
CBorder=None

[Grid Text]
Text="This Part is 1st Amplifier in meter"
Px=1704,80
Height=-18
GridSnap=True
JustifyH=Left
JustifyV=Bottom
CBorder=None

[Grid Text]
Text="VE"
Px=2024,656
GridSnap=True
JustifyH=Left
JustifyV=Bottom
CBorder=None

[Grid Text]
Text="SGND"
Px=1088,144
GridSnap=True
JustifyH=Left
JustifyV=Bottom
CBorder=None

[Grid Text]
Text="Vcoll"
Px=1184,272
GridSnap=True
JustifyH=Left
JustifyV=Bottom
CBorder=None

[Grid Text]
Text="Vemit"
Px=1160,408
GridSnap=True
JustifyH=Left
JustifyV=Bottom
CBorder=None

[Grid Text]
Text="Zero_adj"
Px=1064,88
GridSnap=True
JustifyH=Left
JustifyV=Bottom
CBorder=None

[Grid Text]
Text="Chop1"
Px=808,176
GridSnap=True
JustifyH=Left
JustifyV=Bottom
CBorder=None

[Grid Text]
Text="VC"
Px=1424,96
GridSnap=True
JustifyH=Left
JustifyV=Bottom
CBorder=None

[Grid Text]
Text="SGND"
Px=1544,224
GridSnap=True
JustifyH=Left
JustifyV=Bottom
CBorder=None

[Grid Text]
Text="Chop2"
Px=608,160
GridSnap=True
JustifyH=Left
JustifyV=Bottom
CBorder=None

[Grid Text]
Text="Chop_out"
Px=832,352
GridSnap=True
JustifyH=Left
JustifyV=Bottom
CBorder=None

[Grid Text]
Text="Vin"
Px=296,360
GridSnap=True
JustifyH=Left
JustifyV=Bottom
CBorder=None

[Grid Text]
Text="Vout"
Px=1928,304
GridSnap=True
JustifyH=Left
JustifyV=Bottom
CBorder=None

[Grid Text]
Text="SGND"
Px=2168,616
GridSnap=True
JustifyH=Left
JustifyV=Bottom
CBorder=None

[Grid Text]
Text="SGND"
Px=1288,536
GridSnap=True
JustifyH=Left
JustifyV=Bottom
CBorder=None

[Grid Text]
Text="VE"
Px=1744,656
GridSnap=True
JustifyH=Left
JustifyV=Bottom
CBorder=None

[Grid Text]
Text="VC"
Px=48,32
GridSnap=True
JustifyH=Left
JustifyV=Bottom
Page=3
CBorder=None

[Grid Text]
Text="VC"
Px=1512,336
GridSnap=True
JustifyH=Left
JustifyV=Bottom
CBorder=None

[Grid Text]
Text="VE"
Px=112,32
GridSnap=True
JustifyH=Left
JustifyV=Bottom
Page=3
CBorder=None

[Grid Text]
Text="VE"
Px=1512,272
GridSnap=True
JustifyH=Left
JustifyV=Bottom
CBorder=None

[Grid Text]
Text="VC1"
Px=1552,792
GridSnap=True
JustifyH=Left
JustifyV=Bottom
CBorder=None

[Grid Text]
Text="VE1"
Px=1552,728
GridSnap=True
JustifyH=Left
JustifyV=Bottom
CBorder=None

[Schematic]
CurrentSection 0=0
CurrentSection 1=0
CurrentSection 2=0
CurrentSection 3=0
Splitter.xs=0
Splitter.ys=0
TextQuad=4099
Scale=1.3333333333333333
GridUser=10
ShapeGroups="Main","Euro","Polarity","Main1","Main11","Electrolytic","GroundArrow","DeMorgan"
CalcRMS=False
CalcAVG=False
CalcPeak=False
CalcVoltage=True
DisplayMeasure=Last
ShareScales=True

[Tools]
Pos=Top
FILESAVEASOLD=No
BOM=No
FILEPCB=No
PROBE=Yes
SELECT=Yes
PAN=Yes
COMP=Yes
TEXT=Yes
WIRE=Yes
WIRED=Yes
BUS=Yes
GRAPHIC=Yes
FLOWCHART=Yes
LINE=No
ELLIPSE=No
RECT=No
DIAM=No
ARC=No
PIE=No
TRIANGLE=No
STAR=No
LEFTBRK=No
RIGHTBRK=No
BOTHBRK=No
META=Yes
PARALLELOGRAM=No
FC_PROCESS=No
FC_ALT_PROCESS=No
FC_DECISION=No
FC_DATA=No
FC_PREDEFPROCESS=No
FC_INTERNALSTORAGE=No
FC_DOCUMENT=No
FC_MULTIDOCUMENT=No
FC_TERMINATOR=No
FC_PREPARATION=No
FC_MANUALINPUT=No
FC_MANUALOPERATION=No
FC_CONNECTOR=No
FC_OFFPAGECONNECTOR=No
FC_PUNCHCARD=No
FC_PUNCHEDTAPE=No
FC_SUMMING_JUNCTION=No
FC_OR=No
FC_COLLATE=No
FC_SORT=No
FC_EXTRACT=No
FC_MERGE=No
FC_STORED_DATA=No
FC_DELAY=No
FC_SAS=No
FC_MAGNETIC_DISK=No
FC_DAS=No
FC_DISPLAY=No
SPREAD_SHEET=Yes
POLYCLOS=No
POLYOPEN=No
FLAG=Yes
INFO=Yes
HELP=Yes
HELP_SPICE=No
LINK=Yes
CHECK=Yes
REGION_ENABLE=Yes
TITLE_BLOCK=Yes
DIGTRC=No
DIGTRC2=No
BUILD_COMMAND=Yes
DIGALL=No
GRIDTEXT=Yes
COMPTEXT=Yes
NODE=Yes
MEASURED=Yes
NODEV=Yes
CURRENT=Yes
POWER=Yes
CONDITIN=Yes
PIN=Yes
CONNWARN=Yes
CROSS=Yes
GRID=Yes
BORDER=Yes
BORDERONE=Yes
TITLE=Yes
RUBBER=Yes
PROPERTY=Yes
STEP=Yes
MIRROR=Yes
ROTATE=Yes
FLIPY=Yes
FLIPX=Yes
CIR_MAKEMACRO=No
CLEARCUTWIRE=No
CLIPBOARDCIRPAGE2BMM=No
FINDCOMP=Yes
FIND=Yes
REPEAT=No
REPLACE=No
MODEL=Yes
CIR2CKT=Yes
ATTDISP=Yes
ENABLE=Yes
DISABLE=Yes
ENABLE_WITH=Yes
TOFRONT=Yes
TOBACK=Yes
SELNEXT=Yes
PAGEADD=Yes
PAGEADDTEXT=No
ADDSECTION=No
PAGEDEL=Yes
ZOOMIN=Yes
ZOOMOUT=Yes
AUTOSCALECIR=Yes
GOTOFLAG=Yes
UPLEVEL=Yes
COLOR=Yes
FONT=Yes
STYLE=Yes
DM_LAST=No
DM_RMS=No
DM_AVG=No
DM_PEAK=No
GRID_NONE=No
GRID_NORMAL=No
GRID_BOLD_5=No
GRID_BOLD_6=No
GRID_BOLD_USER=No
GRAPH_PAPER=No
SPLITCIRTEXTH=No
SPLITCIRTEXTV=No
SPACE_SPLITTERS_EVENLY=No
NORMALCIR=No
RENAMEDEFINE=No
RENAMECMP=No
ATTALIGN=No
RESETNODEPOS=No
FIT2STANDARD=No
NODESNAP=No
MOVETEXT=No
TEXTINC=No
TOGGLETEXT=No
TOGGLEMODE=No
TOLERANCE=No
ALIGNAB=No
ALIGNLEFT=Yes
ALIGNCENTER=Yes
ALIGNRIGHT=Yes
ALIGNTOP=Yes
ALIGNMIDDLES=Yes
ALIGNBOTTOM=Yes

[Section]
Index=0
Name="sim"
Type=Main
Enable=True
CurrentPage 0=0
CurrentPage 1=0
CurrentPage 2=0
CurrentPage 3=0
TabSize 0=425
TabSize 1=425
TabSize 2=425
TabSize 3=425

[Page]
Index=0
Section=0
Print=True
Enable=True
Name=Main
PrinterScale=1
Scale 0=1
Scale 1=1
Scale 2=1
SB 3=231,0
Scale 3=1.3333333333333333
Px=1092,140
WinBackGround Color=#FFFFFF
Select Color=#FF0000
Anchor Color=#000000
Select Box Color=#000080
Grid Text Color=Height=-12,FStyle=0,Color=#0000FF,Name=Verdana
Grid Text RTF=False
Grid Text Angle=0
Grid Text GridSnap=True
Grid Text PinIt=False
Grid Text JustifyH=Left
Grid Text JustifyV=Bottom
Grid GradientColor2=None
Grid OutlineThickness=1
Grid OutlineColor=None
Component Color=#0000FF
Attribute Text=Height=-12,FStyle=0,Color=#008000,Name=Verdana
Wire Color=#008000
Bus Color=#008000
Pin Connection=Height=-10,FStyle=0,Color=#FF0000,Name=Arial
Pin Marker Color=#008000
Node Number=Height=-11,FStyle=0,Color=#FF00FF,Name=Arial
Node Voltage Color=Height=-11,FStyle=0,Color=#000000,Name=Arial
Dynamic AC Voltage Color=#E4E4E4
Text Banner Text=Height=-15,FStyle=0,Color=#800000,Name=Arial
Title Block Background=#C0C0C0
Current=Height=-11,FStyle=0,Color=#0000FF,Name=Arial
Power/Condition=Height=-11,FStyle=0,Color=#FF0000,Name=Arial
Digital Path Color=#FF0000
Title Block Border=#000000
Disabled	Color=#C0C0C0
Search Color=#FFFF00
Grid Color=#000000
Graph Paper=#E4E4E4
Digital 0 Color=#000000
Digital R Color=#FFFF00
Digital F Color=#FFFF00
Digital 1 Color=#FF0000
Digital X Color=#C0C0C0
Digital Z Color=#808080
Block Select Color=#51F998

[Page]
Index=1
Section=0
Type=Text
Print=False
Enable=True
Name=Text
Font=Height=-15,FStyle=0,Color=#000000,Name=Courier New
Comment Color=#008000
WinBackGround Color=#FFFFFF
Disabled	Color=#C0C0C0
KeyWord Color=#0000FF
Error	Color=#FF0000
Search Color=#FFFF00

[Page]
Index=2
Section=0
Type=Text
Print=False
Enable=True
Name=Models
Font=Height=-15,FStyle=0,Color=#000000,Name=Courier New
Comment Color=#008000
WinBackGround Color=#FFFFFF
Disabled	Color=#C0C0C0
KeyWord Color=#0000FF
Error	Color=#FF0000
Search Color=#FFFF00

[Page]
Index=3
Section=0
Print=True
Enable=True
Name=Power Supplies
PrinterScale=1
Scale 0=1
Scale 1=1
Scale 2=1
Scale 3=1
Px=111,55
WinBackGround Color=#FFFFFF
Select Color=#FF0000
Anchor Color=#000000
Select Box Color=#000080
Grid Text Color=Height=-12,FStyle=0,Color=#0000FF,Name=Verdana
Grid Text RTF=False
Grid Text Angle=0
Grid Text GridSnap=True
Grid Text PinIt=False
Grid Text JustifyH=Left
Grid Text JustifyV=Bottom
Grid GradientColor2=None
Grid OutlineThickness=1
Grid OutlineColor=None
Component Color=#0000FF
Attribute Text=Height=-12,FStyle=0,Color=#008000,Name=Verdana
Wire Color=#008000
Bus Color=#008000
Pin Connection=Height=-10,FStyle=0,Color=#FF0000,Name=Arial
Pin Marker Color=#008000
Node Number=Height=-11,FStyle=0,Color=#FF00FF,Name=Arial
Node Voltage Color=Height=-11,FStyle=0,Color=#000000,Name=Arial
Dynamic AC Voltage Color=#E4E4E4
Text Banner Text=Height=-15,FStyle=0,Color=#800000,Name=Arial
Title Block Background=#C0C0C0
Current=Height=-11,FStyle=0,Color=#0000FF,Name=Arial
Power/Condition=Height=-11,FStyle=0,Color=#FF0000,Name=Arial
Digital Path Color=#FF0000
Title Block Border=#000000
Disabled	Color=#C0C0C0
Search Color=#FFFF00
Grid Color=#000000
Graph Paper=#E4E4E4
Digital 0 Color=#000000
Digital R Color=#FFFF00
Digital F Color=#FFFF00
Digital 1 Color=#FF0000
Digital X Color=#C0C0C0
Digital Z Color=#808080
Block Select Color=#51F998

[Page]
Index=4
Section=0
Type=Info
Print=False
Enable=True
Name=Info
Font=Height=-15,FStyle=0,Color=#000000,Name=Courier New
Comment Color=#008000
WinBackGround Color=#FFFFFF
Disabled	Color=#C0C0C0
KeyWord Color=#0000FF
Error	Color=#FF0000
Search Color=#FFFF00

[Text Area]
Section=0
Page=1
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
